onibrow/countdown_display/examples/set_time/set_time.ino

// Date and time functions using a DS3231 RTC connected via I2C and Wire lib
#include "RTClib.h"

RTC_DS3231 rtc;
const uint8_t ds_pin = 16;

char daysOfTheWeek[7][12] = {"Sunday", "Monday", "Tuesday", "Wednesday", "Thursday", "Friday", "Saturday"};

void setup () {
  Serial.begin(57600);
  pinMode(ds_pin, OUTPUT);
  digitalWrite(ds_pin, HIGH);

  if (! rtc.begin()) {
    Serial.println("Couldn't find RTC");
    Serial.flush();
    abort();
  }
  rtc.adjust(DateTime(F(__DATE__), F(__TIME__)));
}

void loop () {
  DateTime now = rtc.now();

  Serial.print(now.year(), DEC);
  Serial.print('/');
  Serial.print(now.month(), DEC);
  Serial.print('/');
  Serial.print(now.day(), DEC);
  Serial.print(" (");
  Serial.print(daysOfTheWeek[now.dayOfTheWeek()]);
  Serial.print(") ");
  Serial.print(now.hour(), DEC);
  Serial.print(':');
  Serial.print(now.minute(), DEC);
  Serial.print(':');
  Serial.print(now.second(), DEC);
  Serial.println();

  Serial.print(" since midnight 1/1/1970 = ");
  Serial.print(now.unixtime());
  Serial.print("s = ");
  Serial.print(now.unixtime() / 86400L);
  Serial.println("d");

  // calculate a date which is 7 days and 30 seconds into the future
  DateTime future (now + TimeSpan(7, 12, 30, 6));

  Serial.print(" now + 7d + 30s: ");
  Serial.print(future.year(), DEC);
  Serial.print('/');
  Serial.print(future.month(), DEC);
  Serial.print('/');
  Serial.print(future.day(), DEC);
  Serial.print(' ');
  Serial.print(future.hour(), DEC);
  Serial.print(':');
  Serial.print(future.minute(), DEC);
  Serial.print(':');
  Serial.print(future.second(), DEC);
  Serial.println();

  Serial.print("Temperature: ");
  Serial.print(rtc.getTemperature());
  Serial.println(" C");

  Serial.println();
  delay(3000);
}
